TheSilentDefender/ADC_Board_Aramaki_Lab/ADC/components/designblocks.kicad_blocks/Voltage Divider + Connector.kicad_block/Voltage Divider + Connector.kicad_sch

## KiCad design ADC/components/designblocks.kicad_blocks/Voltage Divider + Connector.kicad_block/Voltage Divider + Connector.kicad_sch (2025-04-09)

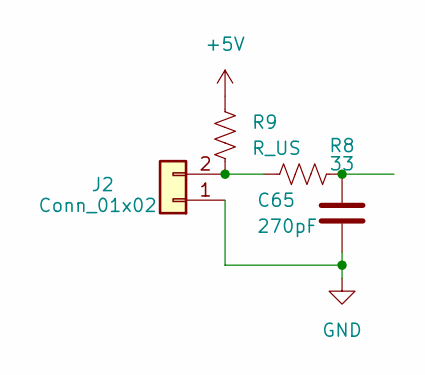
[picture p7: schematic Voltage Divider + Connector.kicad_sch]

Parts:
C65: 270pF; C_0402_1005Metric
J2: Conn_01x02
R8: 33; R_0402_1005Metric_Pad0.72x0.64mm_HandSolder
R9: R_US

Connections:
+5V: R9.1
GND: C65.2, J2.1
unnamed: C65.1, R8.2
unnamed: J2.2, R8.1, R9.2
